radioegor146/vu-meter/front/panel-cutout-300dpi/cutout.png

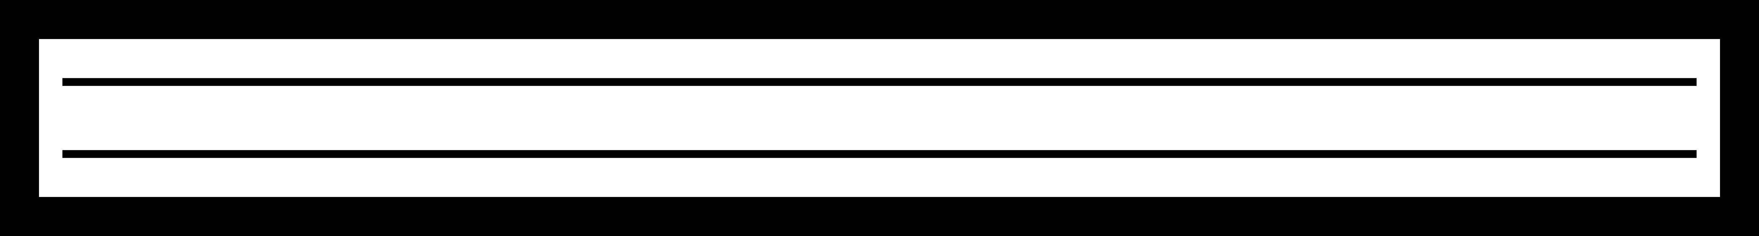
front/panel-cutout-300dpi/cutout.png
